JasperMaes01/Project_Design_Soldering_Station/3D-design/Pictures of the design/Assembly (3).png

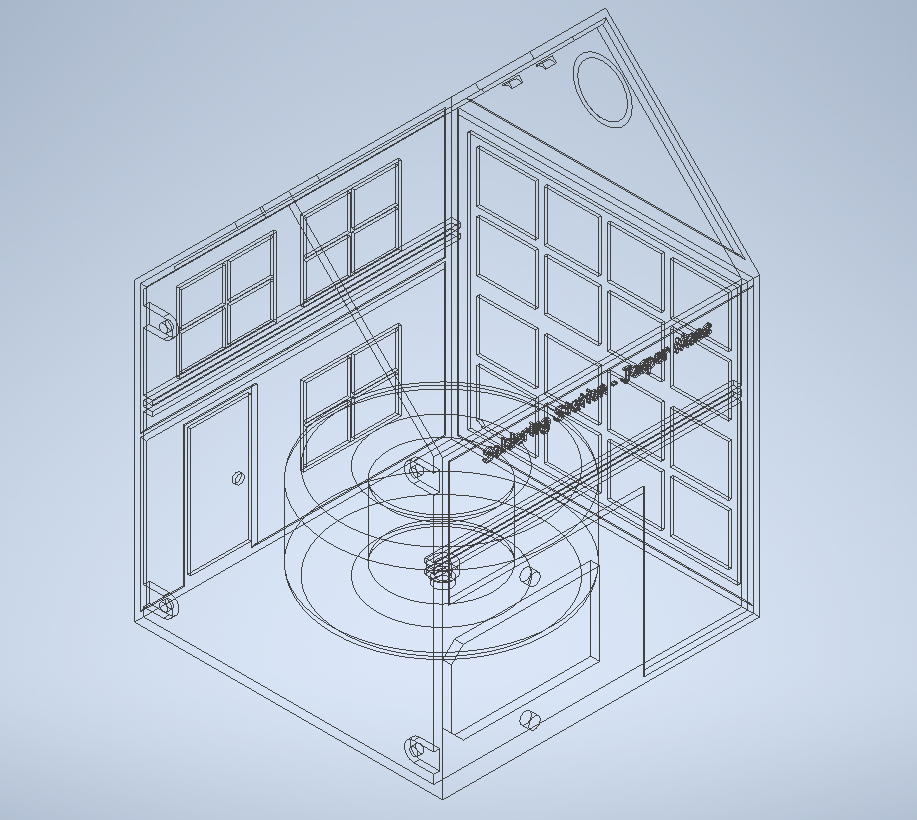
3D-design/Pictures of the design/Assembly (3).png
